Swasthik-FA/Kicad_Template/HTML/3d/Nano-Board-rev-2-3d-angled-bottom.png

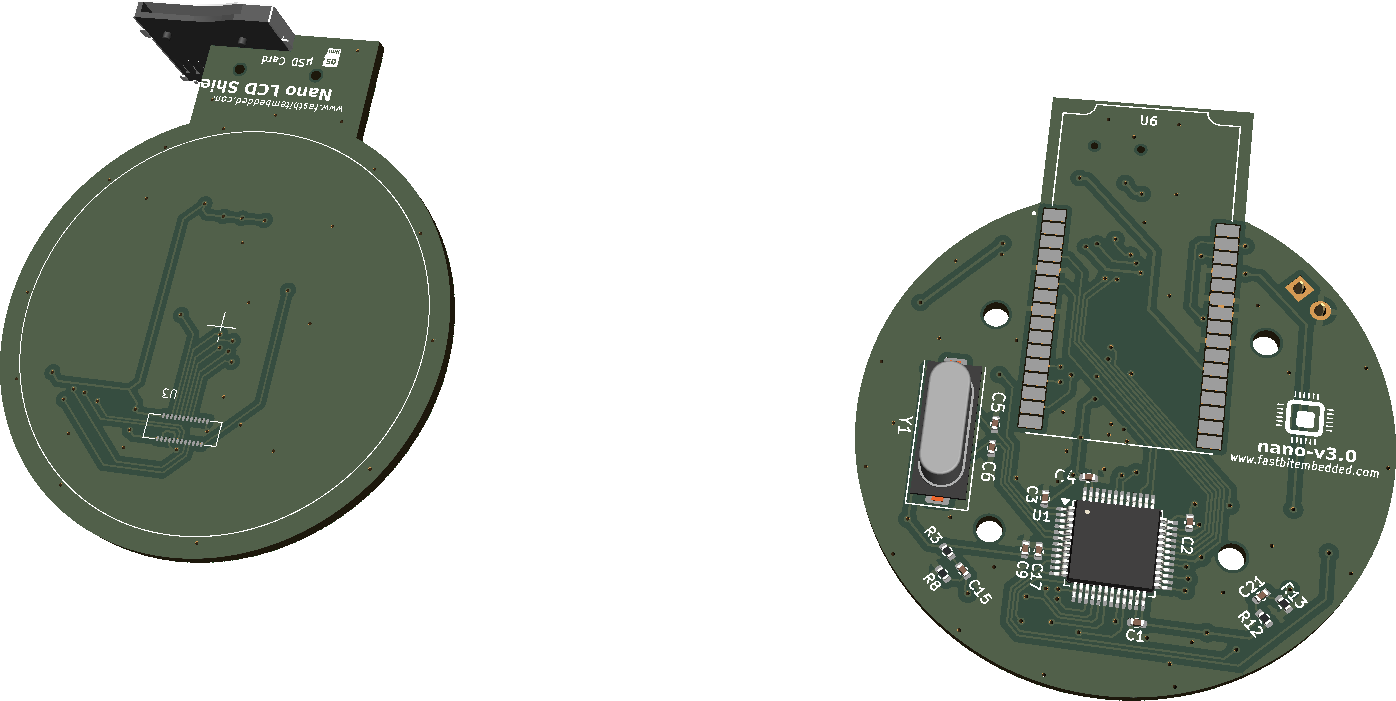
HTML/3d/Nano-Board-rev-2-3d-angled-bottom.png
